clusterzx/MultiController_PCB/Hardware/documentation/T-X20W345372A_JLCPCB/confirm orientation of LED.png

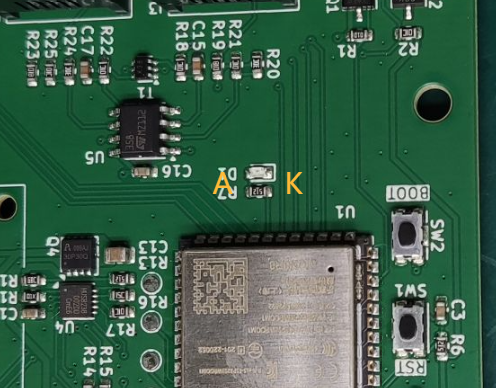
Hardware/documentation/T-X20W345372A_JLCPCB/confirm orientation of LED.png
