clusterzx/MultiController_PCB/Hardware/documentation/T-X20W345372A_JLCPCB/T-X20W345372A (3).jpg

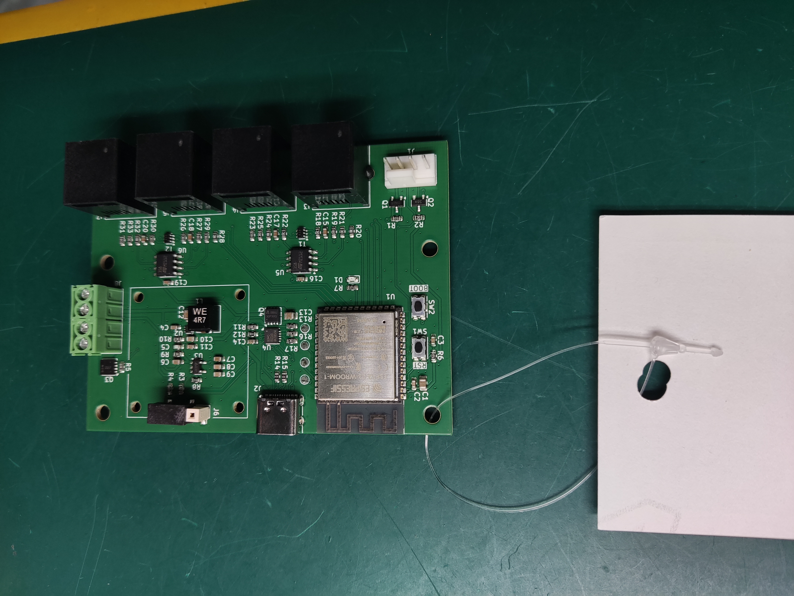
Hardware/documentation/T-X20W345372A_JLCPCB/T-X20W345372A (3).jpg
