clusterzx/MultiController_PCB/Hardware/documentation/TIPowerDesigner_TPS61175_240820.png

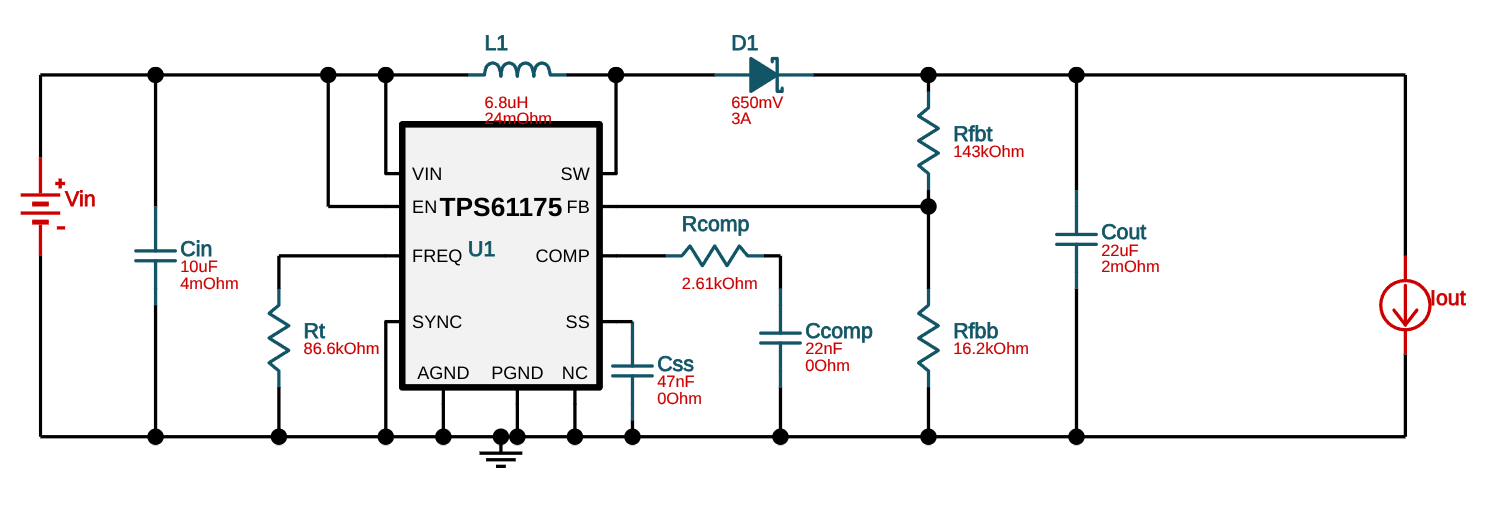
Hardware/documentation/TIPowerDesigner_TPS61175_240820.png
